BasicRespirator/basic/cut n sew mask/sketches and photos/3-4 front.jpg

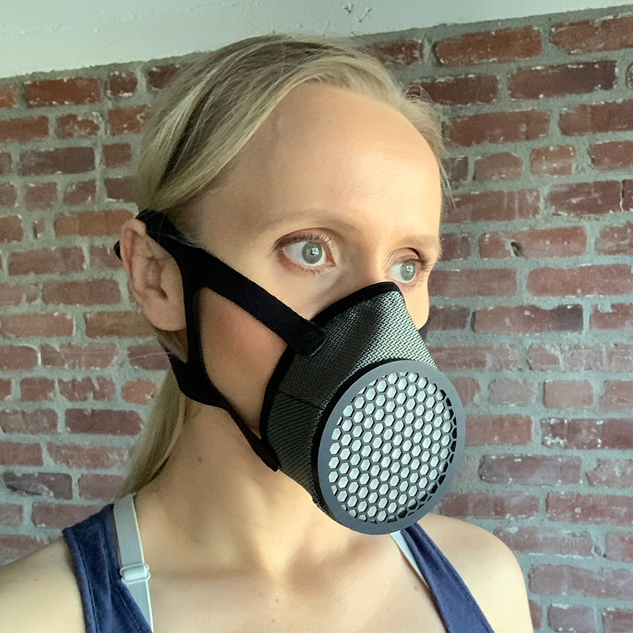
cut n sew mask/sketches and photos/3-4 front.jpg
