BasicRespirator/basic/cut n sew mask/sketches and photos/3-4 rear.jpg

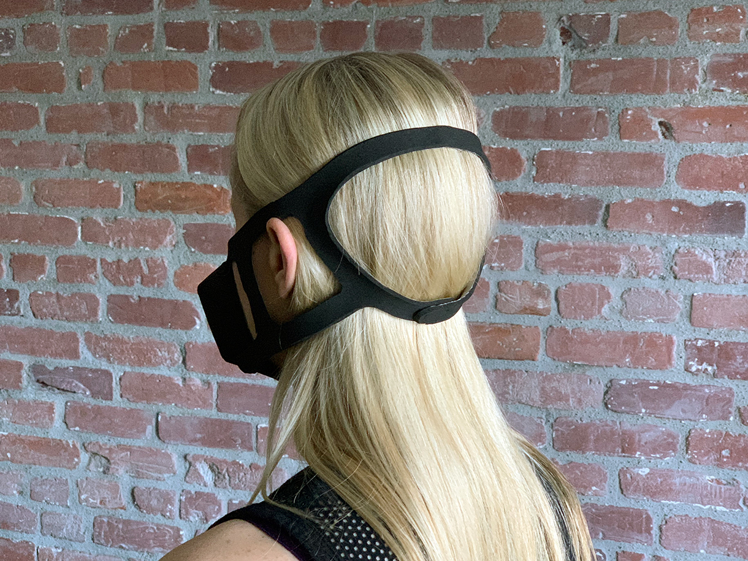
cut n sew mask/sketches and photos/3-4 rear.jpg
