BasicRespirator/basic/cut n sew mask/sketches and photos/cut n sew mask.jpg

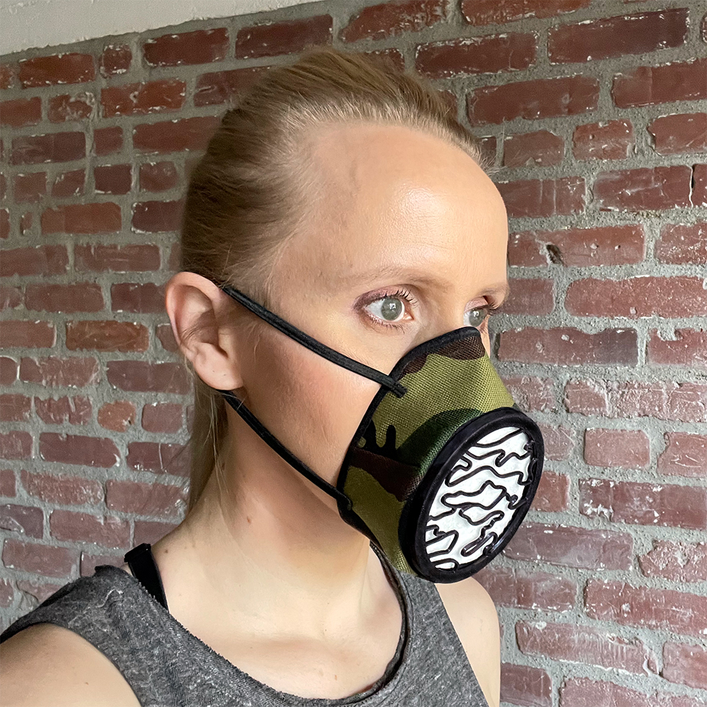
cut n sew mask/sketches and photos/cut n sew mask.jpg
