BasicRespirator/basic/prior versions/65mm Filter Assembly/filter_cap_65_slim.stl

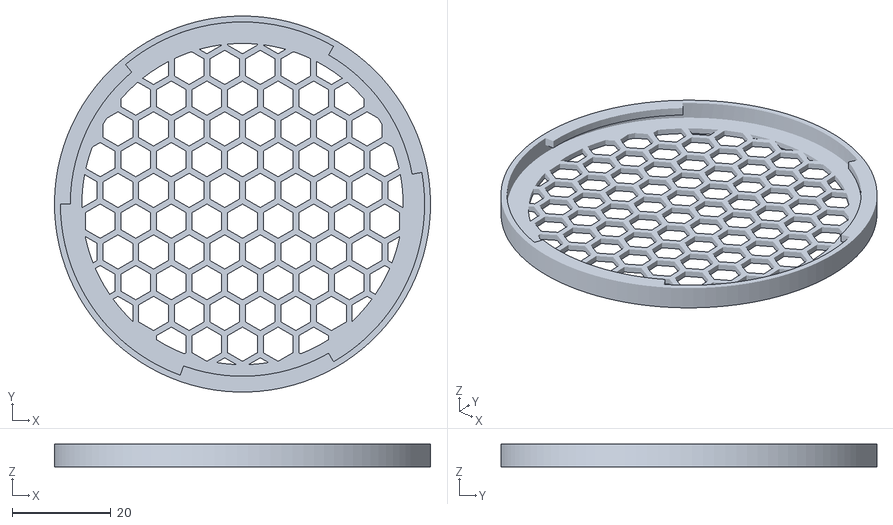
[picture p29: CAD file, 2020-04-17]
prior versions/65mm Filter Assembly/filter_cap_65_slim.stl
76.1 x 76.1 x 4.60
