BasicRespirator/basic/cut n sew mask/prior versions/harness_5-4.dxf

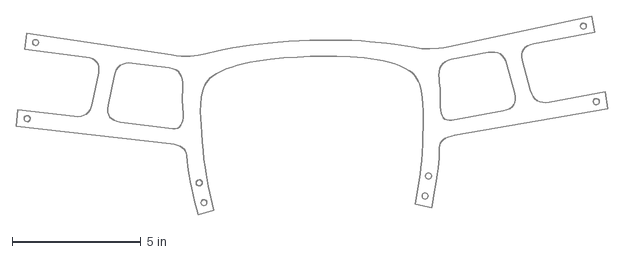
[picture p30: CAD file, 2020-05-05]
cut n sew mask/prior versions/harness_5-4.dxf
22.9 x 7.69 in
