BasicRespirator/basic/prior versions/65mm Filter Assembly/filter_holder_65_slim.stl

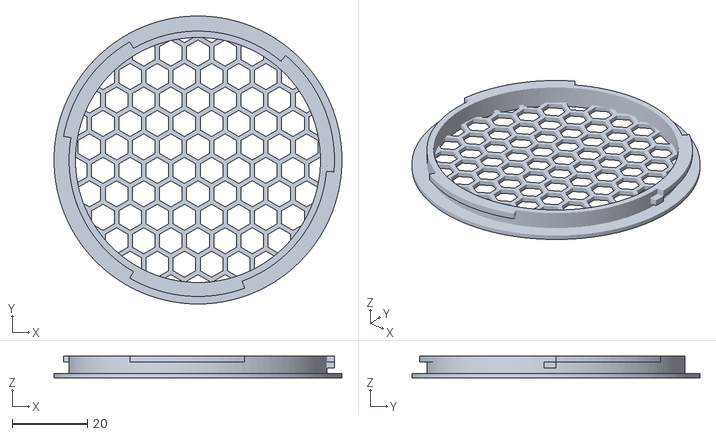
[picture p31: CAD file, 2020-04-17]
prior versions/65mm Filter Assembly/filter_holder_65_slim.stl
76.4 x 76.4 x 5.75
