BasicRespirator/basic/3d printed mask/photos/mask-3-4 front.jpg

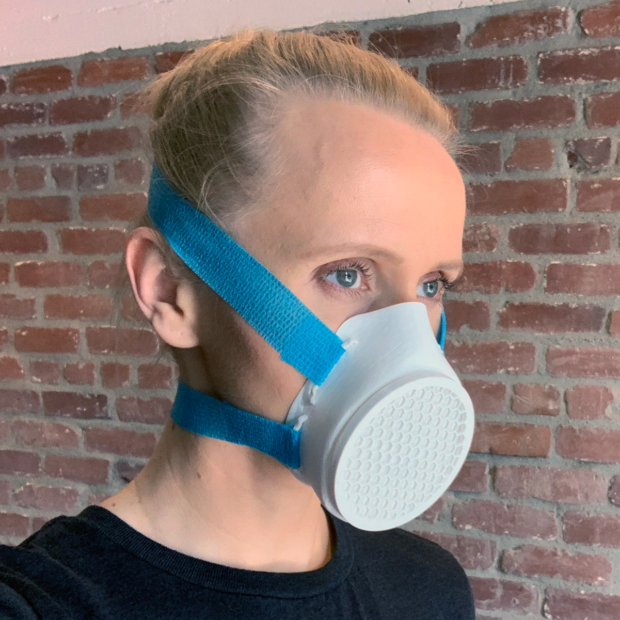
3d printed mask/photos/mask-3-4 front.jpg
